Galactic-Code-Developers/DPPH-Magic-Angle-Ferromagnetism/cad/magic.png

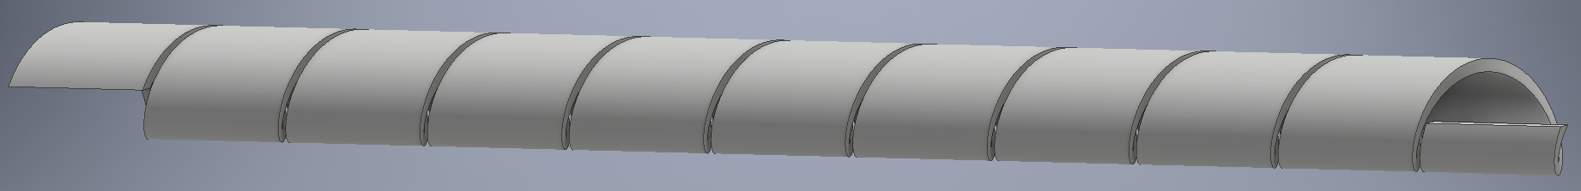
cad/magic.png
