Galactic-Code-Developers/DPPH-Magic-Angle-Ferromagnetism/figures/fig3.png

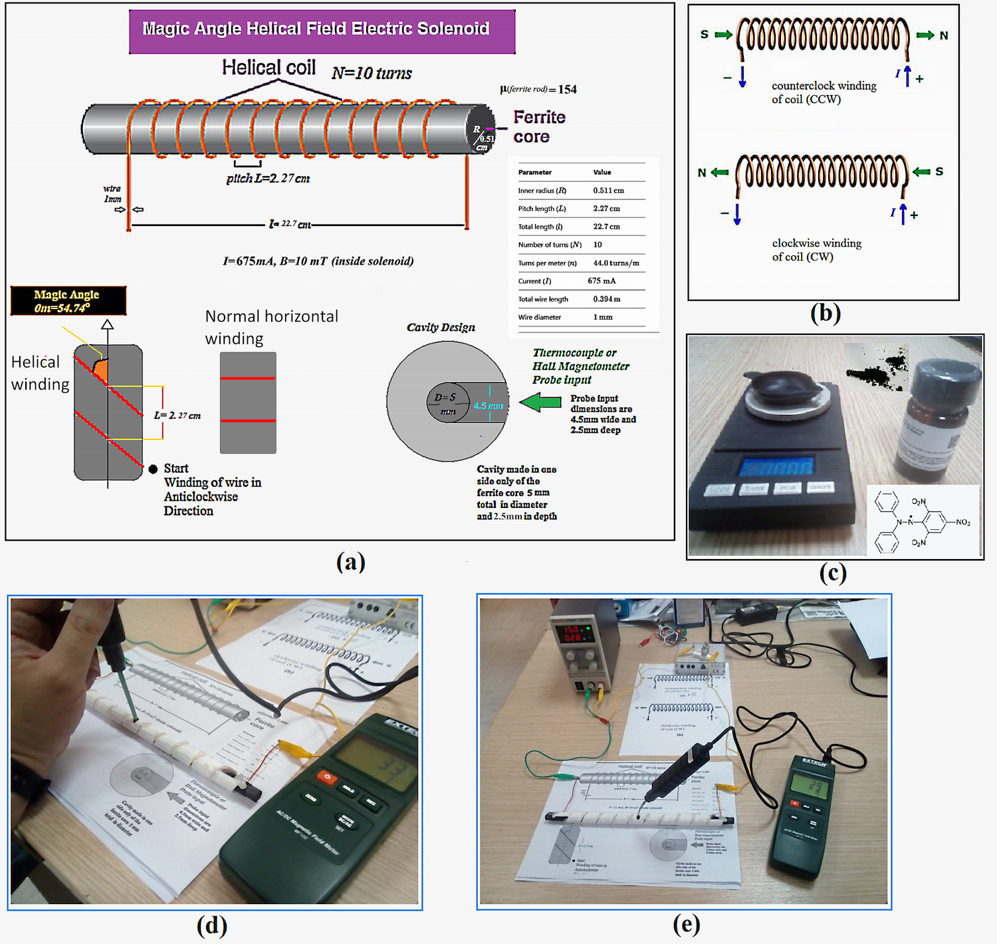
figures/fig3.png
