Galactic-Code-Developers/DPPH-Magic-Angle-Ferromagnetism/figures/fig5.png

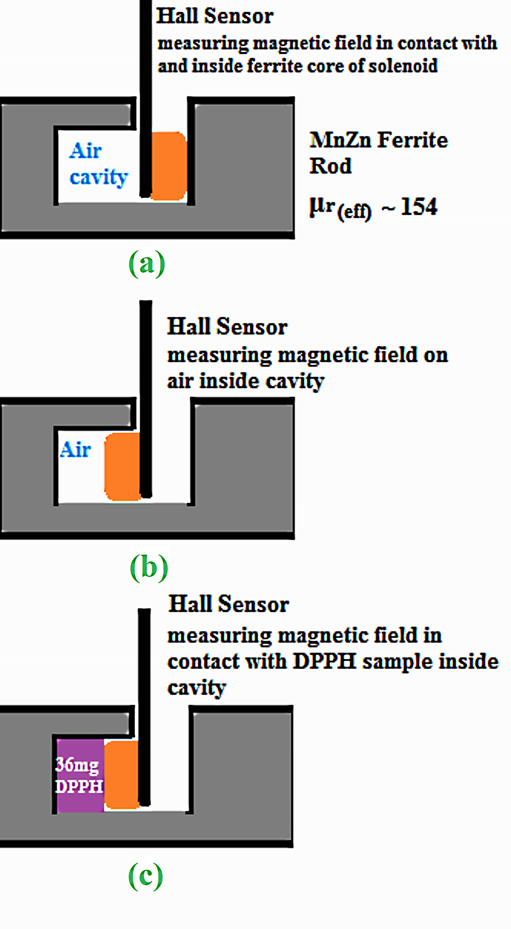
figures/fig5.png
