Galactic-Code-Developers/DPPH-Magic-Angle-Ferromagnetism/figures/fig7.png

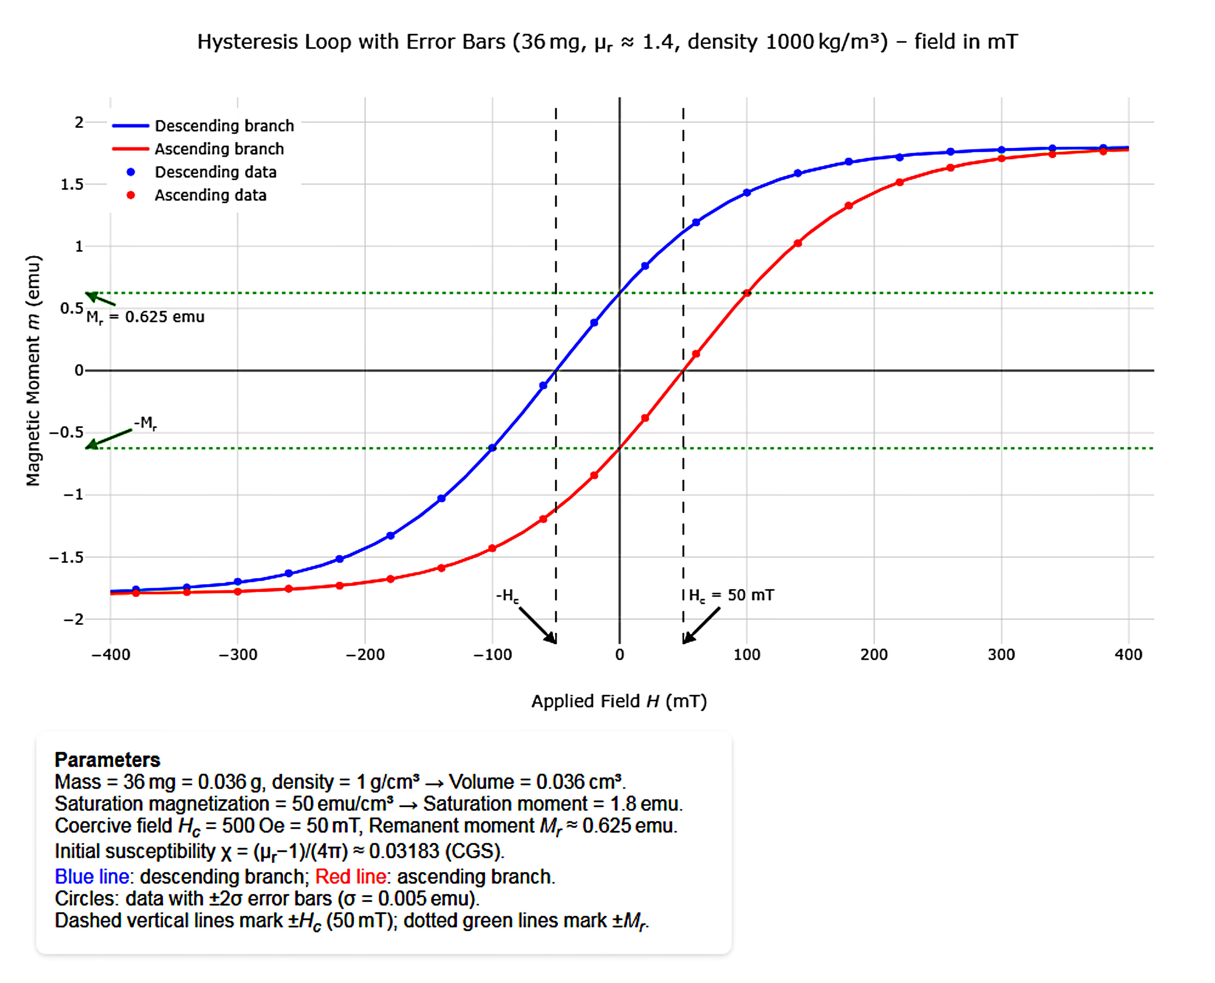
figures/fig7.png
