Galactic-Code-Developers/DPPH-Magic-Angle-Ferromagnetism/figures/samples/CNC drilled cavity + Probe channel on ferrite core demonstration example.jpg

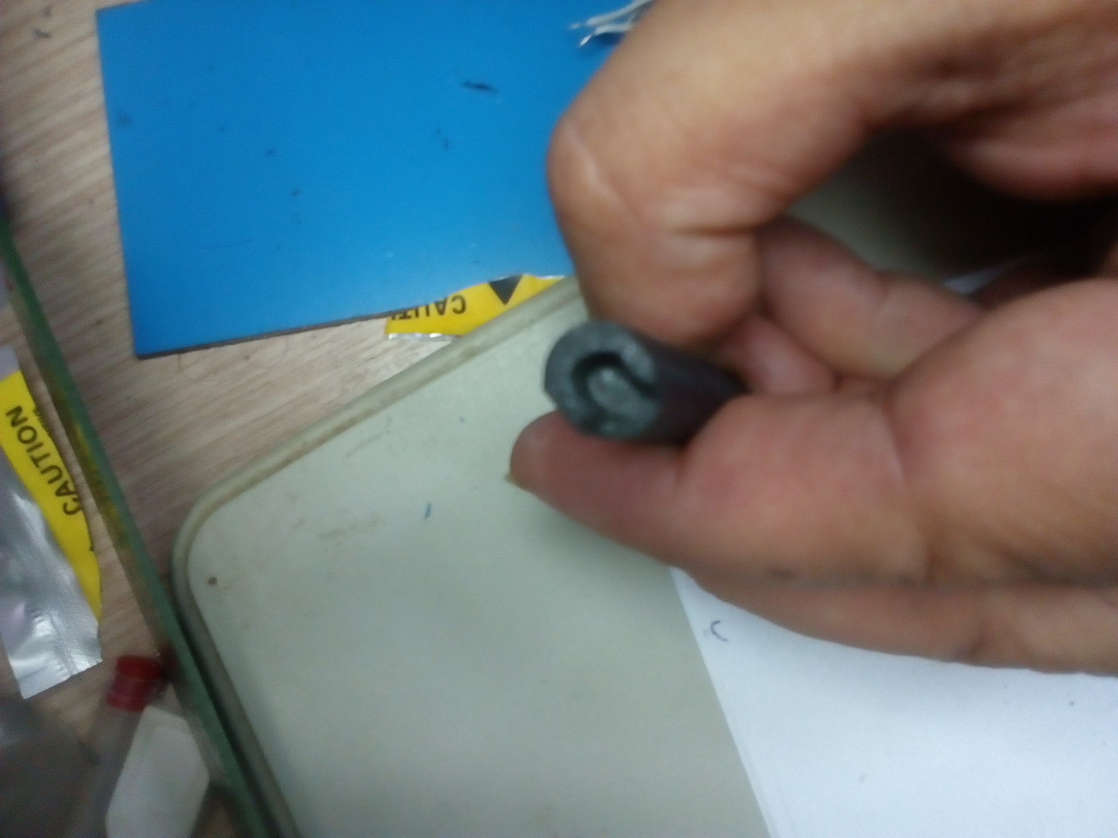
figures/samples/CNC drilled cavity + Probe channel on ferrite core demonstration example.jpg
