Galactic-Code-Developers/DPPH-Magic-Angle-Ferromagnetism/figures/samples/DPPH sample_after exposure_hysteresis_data table .png

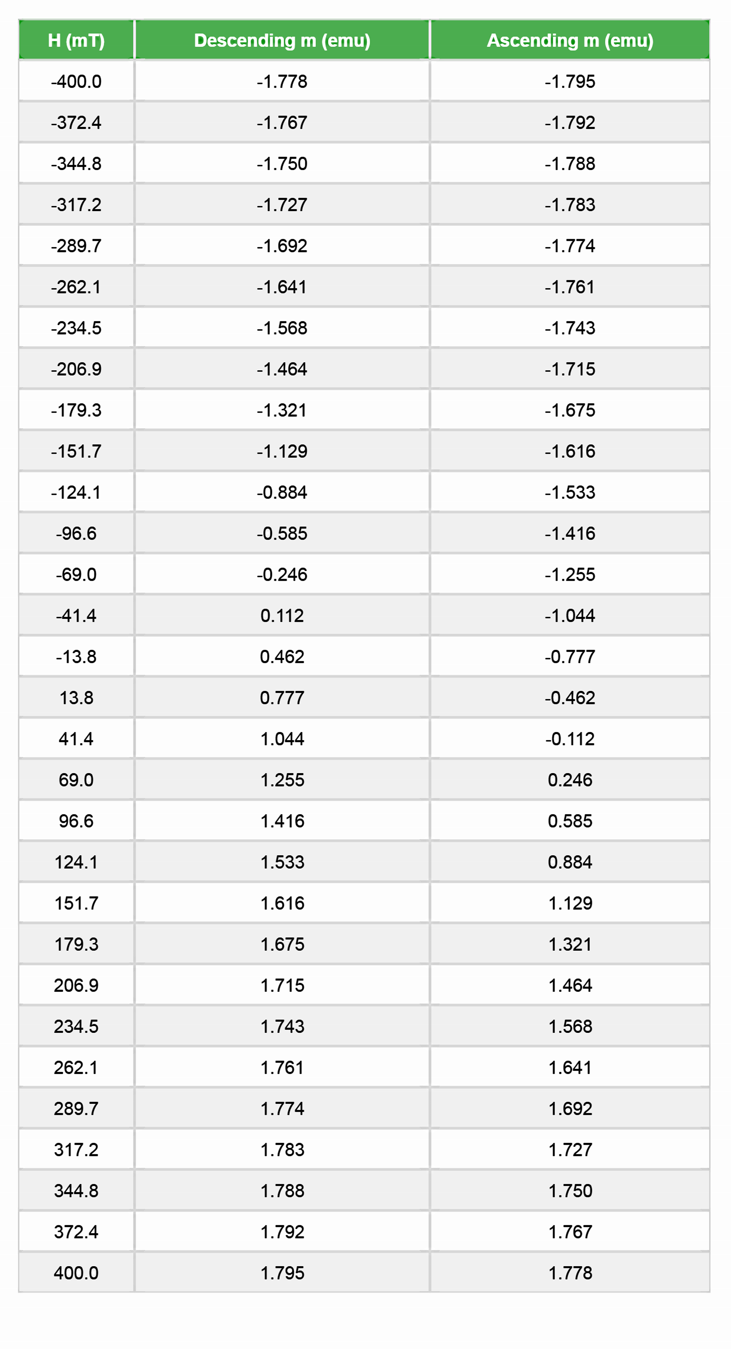
figures/samples/DPPH sample_after exposure_hysteresis_data table .png
