Galactic-Code-Developers/DPPH-Magic-Angle-Ferromagnetism/figures/samples/DPPH Sample_Hysteresis curve_after exposure.png

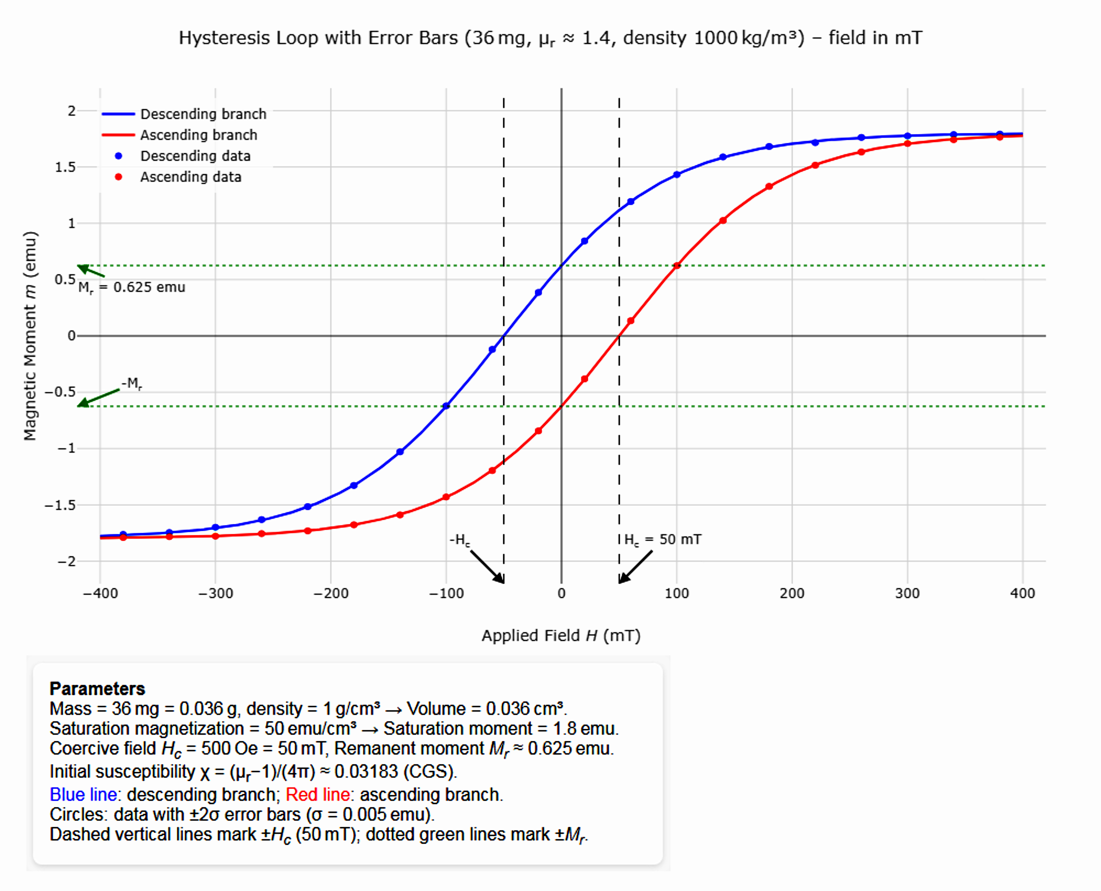
figures/samples/DPPH Sample_Hysteresis curve_after exposure.png
